nickbits1024/EasyKVM/main/keyboard.h

#ifndef KEYBOARD_H
#define KEYBOARD_H

#define KEY_1 0x1e // Keyboard 1 and !
#define KEY_2 0x1f // Keyboard 2 and @
#define KEY_3 0x20 // Keyboard 3 and #
#define KEY_4 0x21 // Keyboard 4 and $
#define KEY_5 0x22 // Keyboard 5 and %
#define KEY_6 0x23 // Keyboard 6 and ^
#define KEY_7 0x24 // Keyboard 7 and &
#define KEY_8 0x25 // Keyboard 8 and *
#define KEY_9 0x26 // Keyboard 9 and (
#define KEY_0 0x27 // Keyboard 0 and )

typedef void* keyboard_handle_t;

esp_err_t keyboard_preinit();
esp_err_t keyboard_init(keyboard_handle_t* kbd_handle);

#endif
